RivasMario/Delta-Split-75/case/left/plate/ALPS LEFT B.dxf

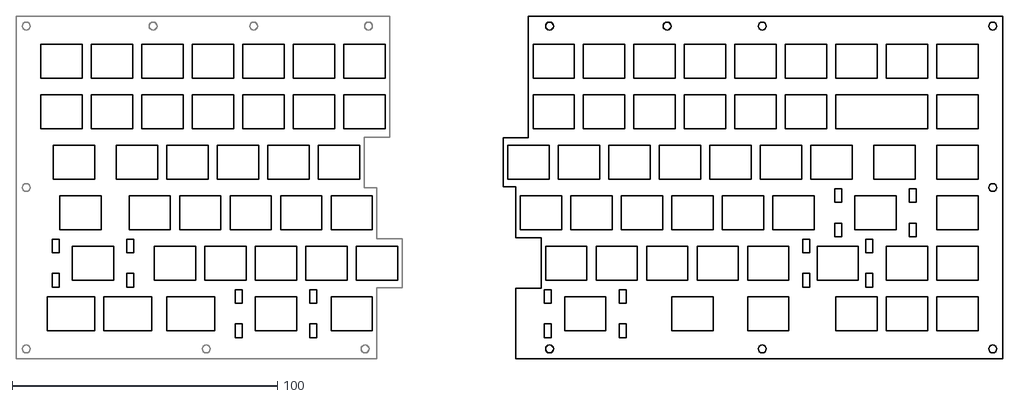
[picture p23: CAD file, 2026-04-20]
case/left/plate/ALPS LEFT B.dxf
372.1 x 129.3
