RivasMario/Delta-Split-75/case/right/plate/ALPS+MX RIGHT B.dxf

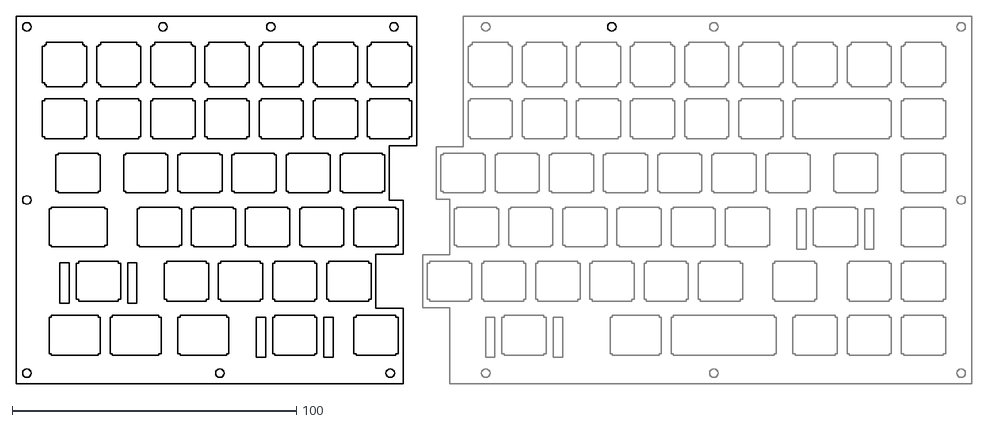
[picture p24: CAD file, 2026-04-20]
case/right/plate/ALPS+MX RIGHT B.dxf
336.1 x 129.3
